Saussy1/3D_PC_SFX/cad/full case.SLDASM

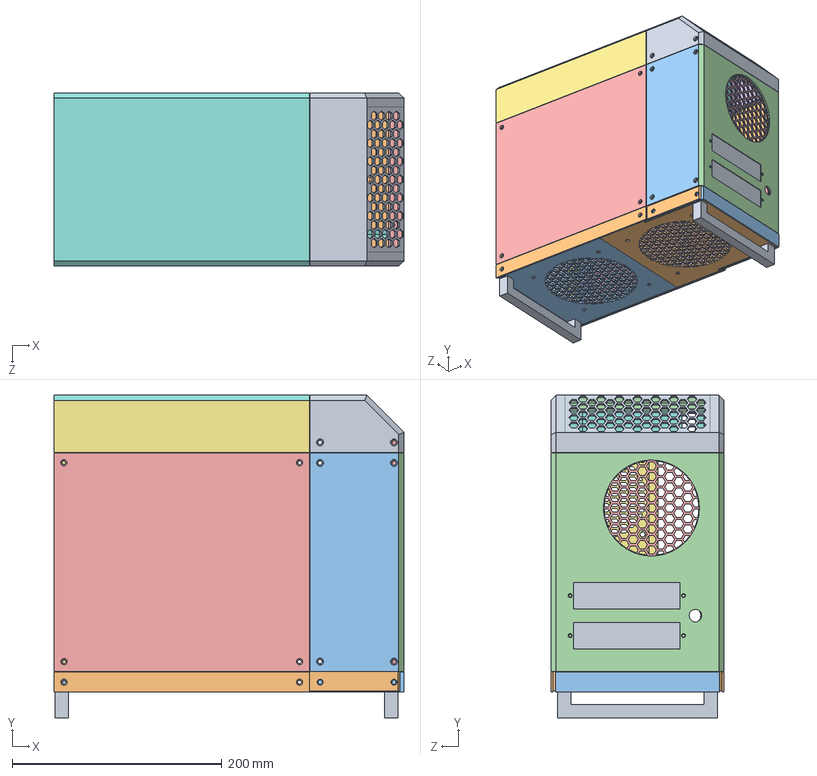
[picture p2: CAD file, 2026-09-24]
cad/full case.SLDASM
333.3 x 307.2 x 165.2 mm
rear_io_frame
matx_s1_frame
front_frame
side_open_frame
bottom_back_frame
bottom_front_frame
foot x 2
psu_bracket
side_frame
matx_s2_frame
top_rear_frame
top_front_frame
bottom_front_panel
bottom_side_panel x 2
psu_cover_panel
top_subpanel
top_left_subpanel
top_right_subpanel
side_panel x 2
front_subpanel
left_subpanel
right_subpanel - Copy
blank_slot x 2
