Saussy1/3D_PC_SFX/cad/frame.SLDASM

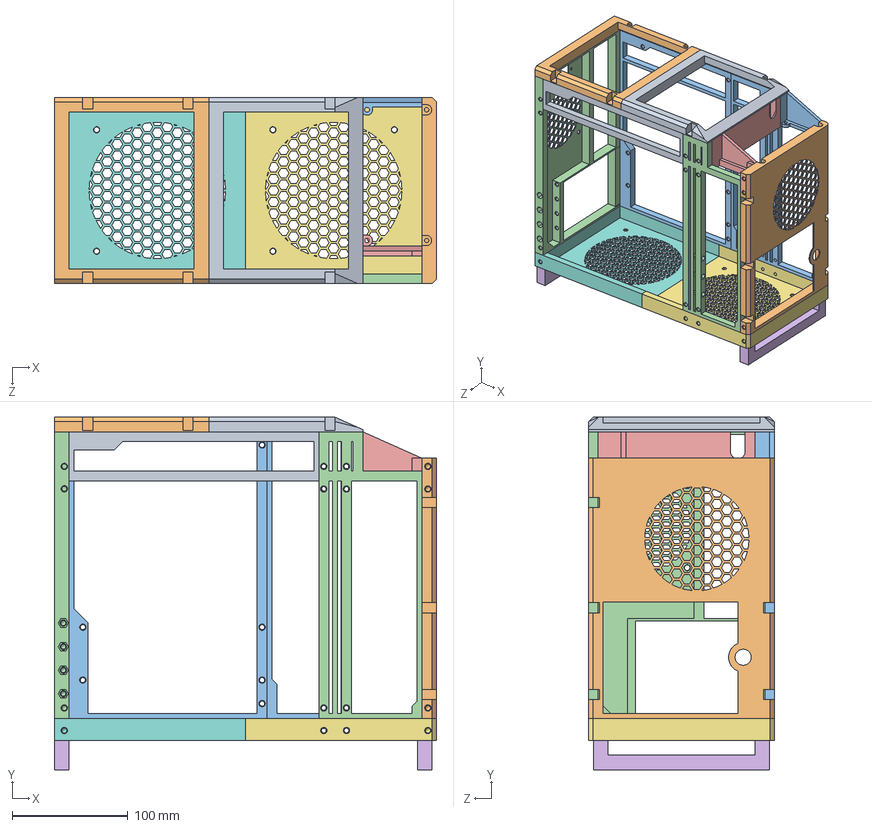
[picture p4: CAD file, 2026-09-24]
cad/frame.SLDASM
330.2 x 304.8 x 160.9 mm
rear_io_frame
matx_s1_frame
front_frame
side_open_frame
bottom_back_frame
bottom_front_frame
foot x 2
psu_bracket
side_frame
matx_s2_frame
top_rear_frame
top_front_frame
