Saussy1/3D_PC_SFX/cad/panels/side_panel.SLDPRT

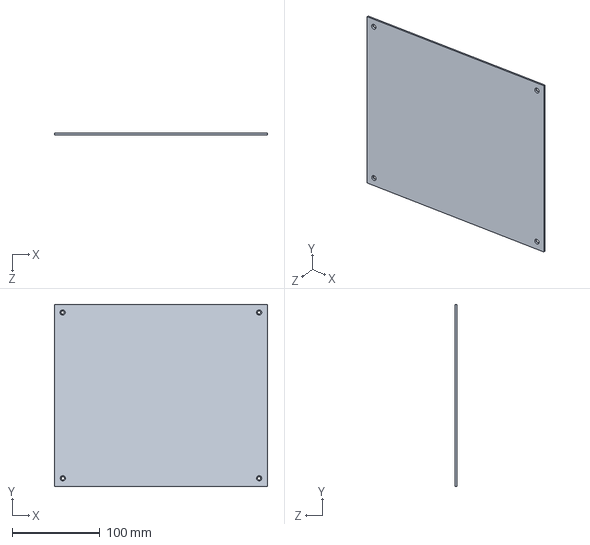
[picture p18: CAD file, 2026-09-24]
cad/panels/side_panel.SLDPRT
243.4 x 208.3 x 1.90 mm
