Saussy1/3D_PC_SFX/cad/pins/pin.SLDPRT

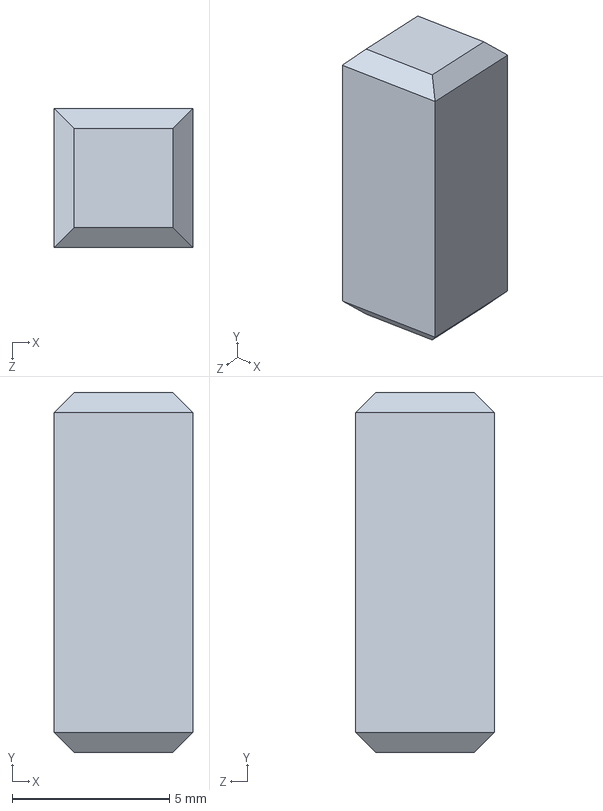
[picture p19: CAD file, 2026-09-21]
cad/pins/pin.SLDPRT
4.40 x 11.4 x 4.40 mm
