Saussy1/3D_PC_SFX/cad/frame/bottom_front_frame.SLDPRT

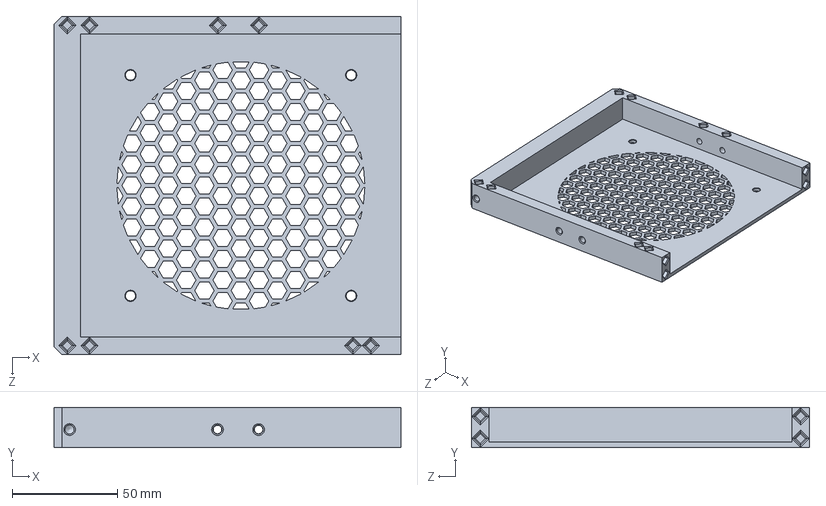
[picture p20: CAD file, 2026-09-24]
cad/frame/bottom_front_frame.SLDPRT
165.1 x 19.1 x 160.9 mm
