Saussy1/3D_PC_SFX/cad/frame/front_frame.SLDPRT

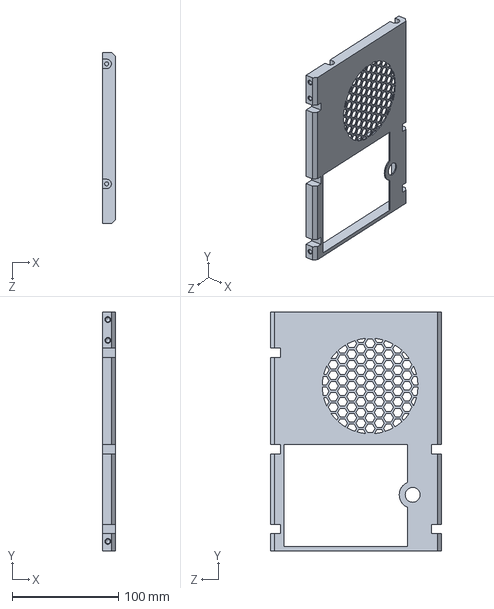
[picture p21: CAD file, 2026-09-24]
cad/frame/front_frame.SLDPRT
12.7 x 224.9 x 160.9 mm
