Saussy1/3D_PC_SFX/cad/panels/bottom_front_panel.SLDPRT

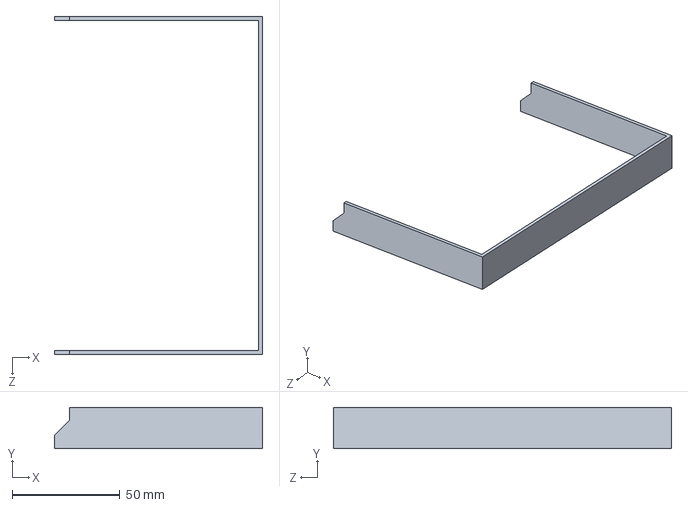
[picture p22: CAD file, 2026-09-24]
cad/panels/bottom_front_panel.SLDPRT
96.4 x 19.1 x 156.6 mm
