Saussy1/3D_PC_SFX/cad/frame/top_rear_frame.SLDPRT

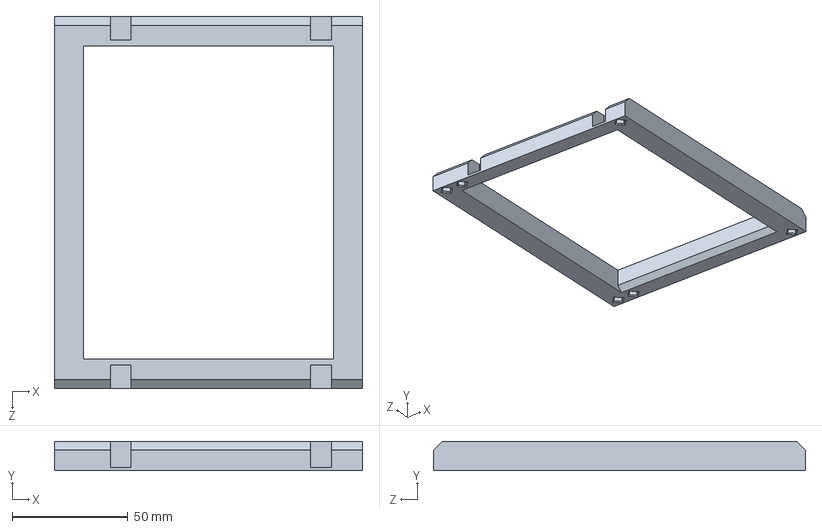
[picture p23: CAD file, 2026-09-24]
cad/frame/top_rear_frame.SLDPRT
133.4 x 12.7 x 160.9 mm
