Saussy1/3D_PC_SFX/cad/panels/bottom_side_panel.SLDPRT

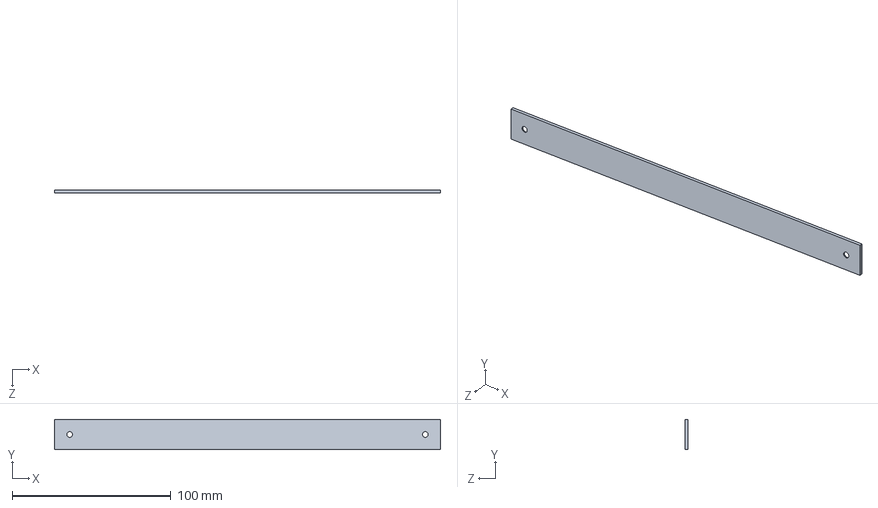
[picture p24: CAD file, 2026-09-21]
cad/panels/bottom_side_panel.SLDPRT
243.4 x 19.1 x 1.90 mm
