Saussy1/3D_PC_SFX/cad/frame/side_open_frame.SLDPRT

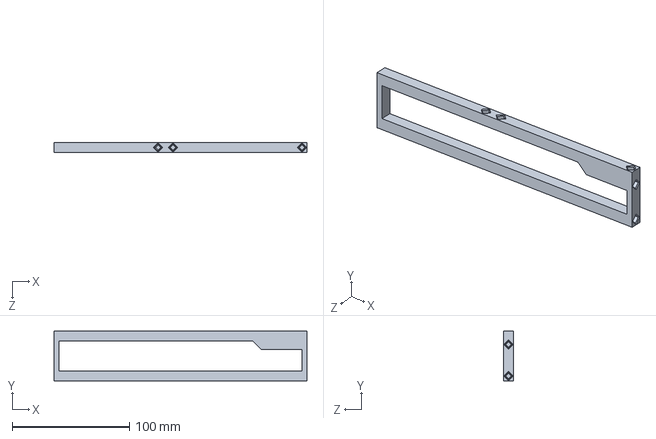
[picture p25: CAD file, 2026-09-21]
cad/frame/side_open_frame.SLDPRT
215.9 x 42.3 x 8.47 mm
