Saussy1/3D_PC_SFX/cad/frame/matx_s1_frame.SLDPRT

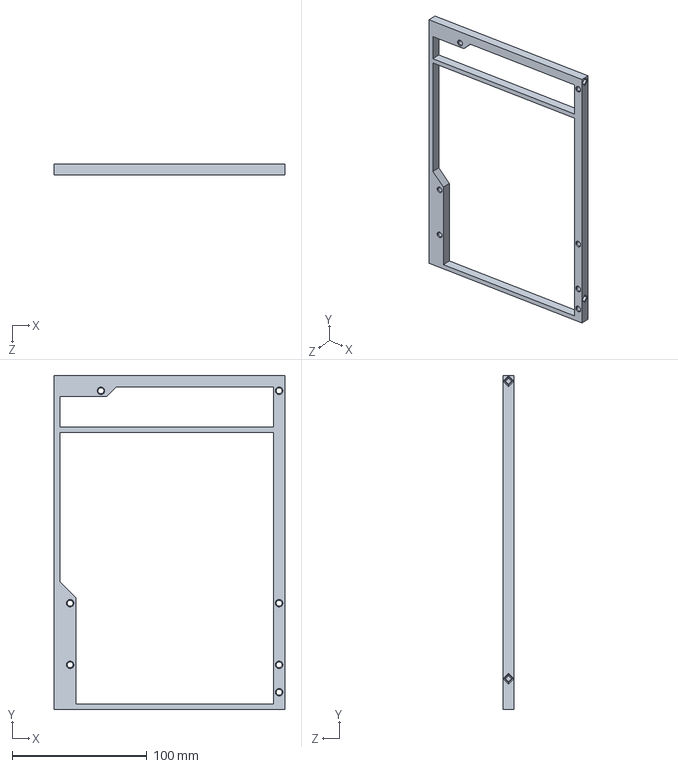
[picture p26: CAD file, 2026-09-21]
cad/frame/matx_s1_frame.SLDPRT
171.0 x 247.6 x 8.47 mm
