Saussy1/3D_PC_SFX/cad/frame/side_frame.SLDPRT

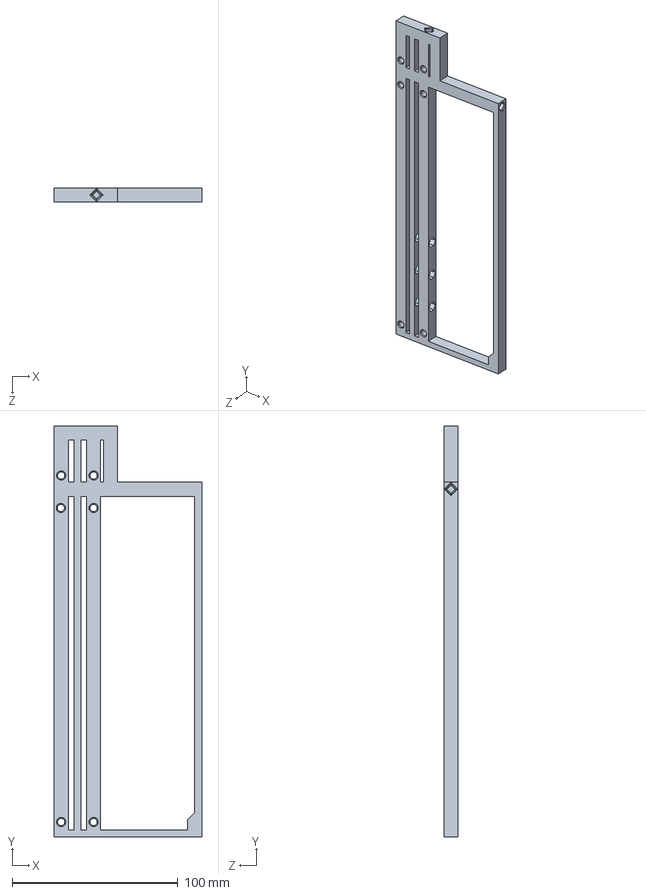
[picture p27: CAD file, 2026-09-21]
cad/frame/side_frame.SLDPRT
88.9 x 247.6 x 8.47 mm
