Saussy1/3D_PC_SFX/cad/frame/foot.SLDPRT

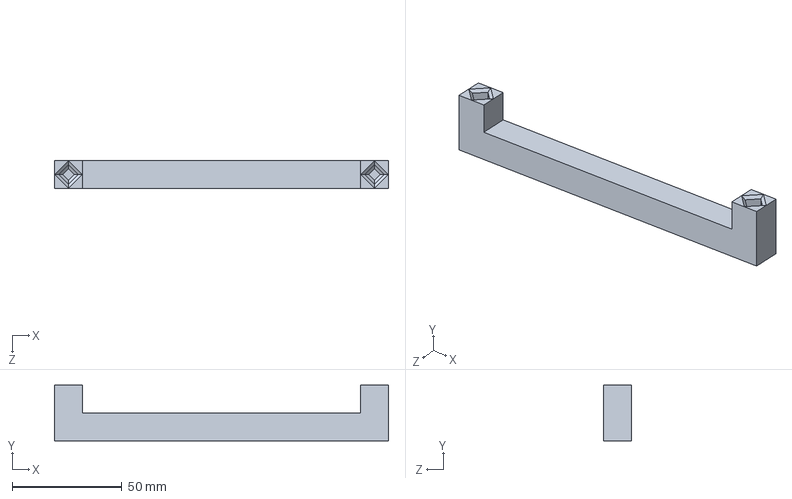
[picture p28: CAD file, 2026-09-21]
cad/frame/foot.SLDPRT
152.4 x 25.4 x 12.7 mm
