Saussy1/3D_PC_SFX/cad/frame/bottom_back_frame.SLDPRT

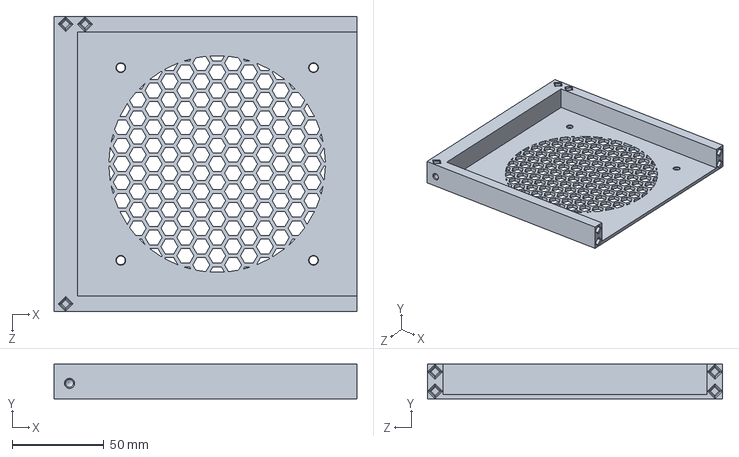
[picture p29: CAD file, 2026-09-21]
cad/frame/bottom_back_frame.SLDPRT
165.1 x 19.1 x 160.9 mm
