Saussy1/3D_PC_SFX/cad/frame/rear_io_frame.SLDPRT

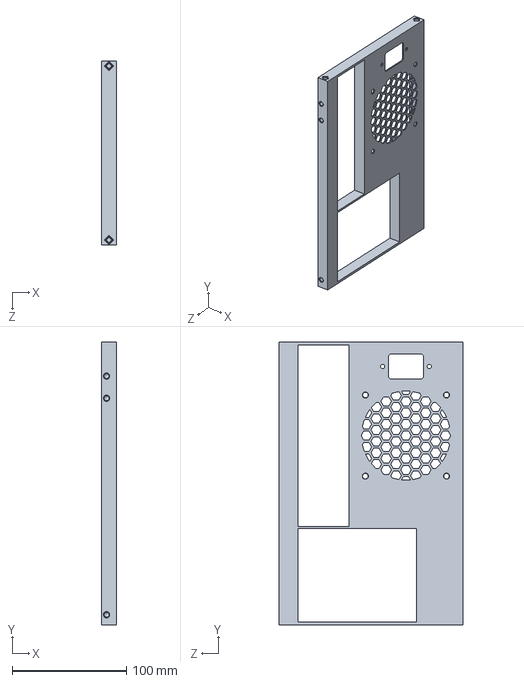
[picture p30: CAD file, 2026-09-21]
cad/frame/rear_io_frame.SLDPRT
12.7 x 247.6 x 160.9 mm
